robouden/PomeloCore-KiCad/Polemo Core/bGeigieScint/firmware/PomeloCore/PomeloCore/src/nvm_params.c

#include "nvm_params.h"

// 5D3D2A1551544E4A4A202020FF0E1F2A
const uint16_t pMove[1024][9] __attribute__((section(".eepSection"))) = {{0,0,0,0,0,0,0,0,0,},{0,0,0,0,0,0,0,0,0,},{0,0,0,0,0,0,0,0,0,},{0,0,0,0,0,0,0,0,0,},{0,0,0,0,0,0,0,0,0,},{0,0,0,0,0,0,0,0,0,},{0,0,0,0,0,0,0,0,0,},{0,0,0,0,0,0,0,0,0,},{0,0,0,0,0,0,0,0,0,},{0,0,18812,32806,128,128,128,128,128,},{0,18866,32799,32799,1241,1241,1241,1241,1241,},{18901,32823,32823,32823,1219,1219,1219,1219,1219,},{28722,30674,30674,30674,1024,1024,1024,1890,3198,},{11264,11264,11264,11264,318,2736,11912,21938,21938,},{0,0,0,0,0,0,0,0,0,},{0,0,0,0,0,0,0,0,0,},{0,0,0,0,0,0,0,0,0,},{0,0,0,0,0,0,0,0,0,},{6791,18950,31783,32813,789,789,789,789,789,},{5954,12349,12349,12349,323,323,323,323,20740,},{2904,2904,2904,2904,1725,1725,1725,14523,31587,},{0,0,0,0,448,448,14624,33226,33226,},{0,0,0,0,376,14594,33195,33195,33195,},{0,0,0,0,0,0,0,0,0,},{0,0,0,0,0,0,0,0,0,},{0,0,14198,32840,639,639,639,639,639,},{0,14215,32850,32850,504,504,504,504,504,},{5744,14060,14060,14060,1956,1956,1956,1956,20679,},{5747,5747,5747,5747,2163,2163,2163,16378,29199,},{0,0,0,0,992,992,18164,33770,33770,},{0,0,0,0,1130,18283,33897,33897,33897,},{0,0,0,0,0,0,0,0,0,},{0,0,0,0,0,0,0,0,0,},{0,0,17162,32789,780,780,780,780,780,},{0,17139,32767,32767,1798,1798,1798,1798,1798,},{13995,26654,26654,26654,1382,1382,1382,1382,7514,},{16020,16020,16020,16020,2439,2439,2439,10723,19195,},{0,0,0,0,710,710,16977,33539,33539,},{0,0,0,0,807,17051,33574,33574,33574,},{0,0,0,0,0,0,0,0,0,},{0,0,0,0,0,0,0,0,0,},{0,0,16237,32767,173,173,173,173,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
